sparkfun/GraphicLCD_Serial_Backpack/Firmware/AVR_Firmware/lcd.h

/***************************************************************************
lcd.h

Function prototypes for the LCD code. Also includes character maps, the
 SparkFun logo, and masks and sprites for the sprite drawing funcitonality.

02 May 2013 - Mike Hord, SparkFun Electronics

This code is released under the Creative Commons Attribution Share-Alike 3.0
 license. You are free to reuse, remix, or redistribute it as you see fit,
 so long as you provide attribution to SparkFun Electronics.

***************************************************************************/

#ifndef __lcd_h
#define __lcd_h

// Yo dawg. Include files in include files is generally a frowned-upon
//  practice; in this case, I'm doing it because I need the definition of
//  the PIX_VAL typedef from glcdbp.h and the PROGMEM support provided in
//  pgmspace.h. Do as I say, not as I do.

#include <avr/pgmspace.h> 
#include "glcdbp.h"

void		lcdConfig(void);
void		lcdClearScreen(void);
void 		lcdDrawPixel(uint8_t x, uint8_t y, PIX_VAL pixel);
void 		lcdDrawLine(uint8_t p1x, uint8_t p1y, uint8_t p2x, uint8_t p2y, PIX_VAL pixel);
void 		lcdDrawCircle(uint8_t x0, uint8_t y0, uint8_t r, PIX_VAL pixel);
void		lcdDrawBox(uint8_t p1x, uint8_t p1y, uint8_t p2x, uint8_t p2y, PIX_VAL pixel);
void		lcdDrawChar(char printMe);
void    lcdDrawLogo(void);
void    lcdEraseBlock(uint8_t x0, uint8_t y0, uint8_t x1, uint8_t y1);
void    lcdGetDataBlock(uint8_t x, uint8_t y, uint8_t *buffer);
void    lcdDrawSprite(uint8_t x, uint8_t y, uint8_t sprite, char angle, PIX_VAL pixel);

// Sprite maps for characters. Lifted from the original glcd code, which in turn
//   lifted them from something called "Sinister 7". I don't know what that is.
//   What I *do* know is that the original codes were upside-down, and I had
//   to write a python script to reverse the bit order of these bitmaps.
static char characterArray[475] PROGMEM = {
	0x00,0x00,0x00,0x00,0x00,/*space*/
	0x00,0x6f,0x6f,0x00,0x00,/*!*/
	0x00,0x07,0x00,0x07,0x00,/*"*/
	0x14,0x7f,0x14,0x7f,0x14,/*#*/
	0x00,0x26,0x6b,0x2a,0x10,/*$*/
	0x43,0x33,0x08,0x64,0x63,/*%*/
	0x32,0x4d,0x49,0x36,0x50,/*&*/
	0x00,0x00,0x07,0x00,0x00,/*'*/
	0x00,0x1c,0x22,0x41,0x00,/*(*/
	0x00,0x41,0x22,0x1c,0x00,/*)*/
	0x11,0x0a,0x1f,0x0a,0x11,/***/
	0x10,0x10,0x7c,0x10,0x10,/*+*/
	0x00,0x00,0xa0,0x60,0x00,/*,*/
	0x10,0x10,0x10,0x10,0x10,/*-*/
	0x00,0x00,0x60,0x60,0x00,/*.*/
	0x40,0x30,0x08,0x06,0x01,/*/*/
	0x3e,0x51,0x49,0x45,0x3e,/*0*/
	0x00,0x42,0x7f,0x40,0x00,/*1*/
	0x42,0x61,0x51,0x49,0x46,/*2*/
	0x22,0x41,0x49,0x49,0x36,/*3*/
	0x08,0x0c,0x0a,0x7f,0x08,/*4*/
	0x27,0x45,0x45,0x45,0x39,/*5*/
	0x3c,0x4a,0x49,0x49,0x30,/*6*/
	0x01,0x61,0x19,0x07,0x01,/*7*/
	0x36,0x49,0x49,0x49,0x36,/*8*/
	0x06,0x49,0x49,0x29,0x1e,/*9*/
	0x00,0x00,0x6c,0x6c,0x00,/*:*/
	0x00,0x00,0xac,0x6c,0x00,/*;*/
	0x08,0x14,0x22,0x41,0x00,/*<*/
	0x14,0x14,0x14,0x14,0x14,/*=*/
	0x00,0x41,0x22,0x14,0x08,/*>*/
	0x02,0x01,0x51,0x09,0x06,/*?*/
	0x3e,0x41,0x5d,0x5d,0x46,/*@*/
	0x7c,0x12,0x11,0x12,0x7c,/*A*/
	0x7f,0x49,0x49,0x49,0x36,/*B*/
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
  0xff, 0xff, 0xff, 0xff, 0xff, 0xff, 0xff, 0xff,
  0xff, 0xff, 0xff, 0xff, 0xff, 0xff, 0xff, 0xff,
  0xff, 0xff, 0xff, 0xff, 0xff, 0xff, 0xff, 0xff,
  0xff, 0xff, 0xff, 0xff, 0xff, 0xff, 0xff, 0xff,
  0xff, 0xff, 0xff, 0xff, 0xff, 0xff, 0xff, 0xff,
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
  };
