sparkfun/GraphicLCD_Serial_Backpack/Firmware/AVR_Firmware/interrupts.c

/***************************************************************************
interrupts.c

Interrupt definition file for the serial graphical LCD backpack project. The
 only actual interrupt handler is the serial receive handler. It lives here.

02 May 2013 - Mike Hord, SparkFun Electronics

This code is released under the Creative Commons Attribution Share-Alike 3.0
 license. You are free to reuse, remix, or redistribute it as you see fit,
 so long as you provide attribution to SparkFun Electronics.

***************************************************************************/

#include <AVR/interrupt.h>
#include "glcdbp.h"

extern volatile uint8_t 	rxRingBuffer[BUF_DEPTH];
extern volatile uint16_t 	rxRingHead;
extern volatile uint16_t	rxRingTail;
extern volatile uint8_t	 bufferSize;

// Handler for USART receive interrupts. This is basically just a stack push
//  for the FIFO we use to store incoming commands. Note that there is no
//  overflow; that might be a nice touch but so far, I haven't even come close
//  to hitting the buffer depth. In fact, I've never exceeded a depth of more
//  than two or three bytes.
ISR(USART_RX_vect)
{
	if (rxRingHead == BUF_DEPTH) rxRingHead = 0;
	bufferSize++;
	rxRingBuffer[rxRingHead++] = UDR0;
}
